jareddilley/LED-Settlers-of-Catan/Print files/reflector.stl

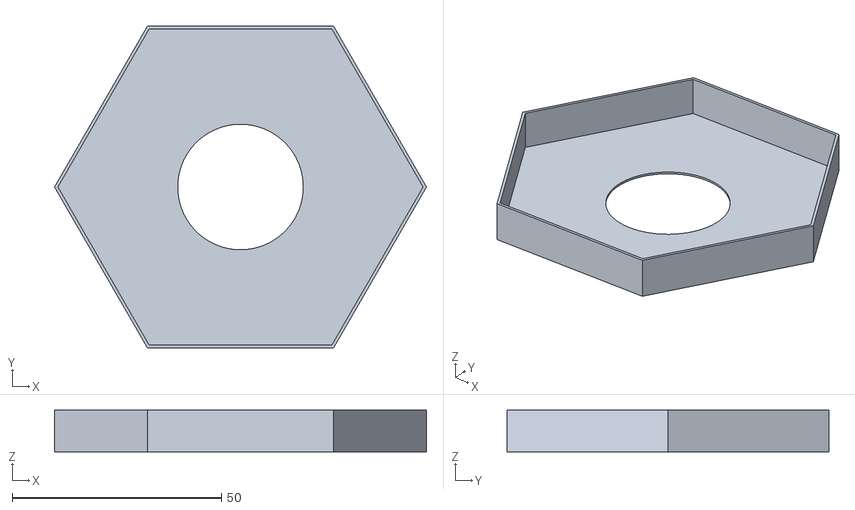
[picture p17: CAD file, 2022-12-04]
Print files/reflector.stl
88.9 x 77.0 x 10.0
